paenian/sand-table/software/sand_trace/example_code/dog.JPG

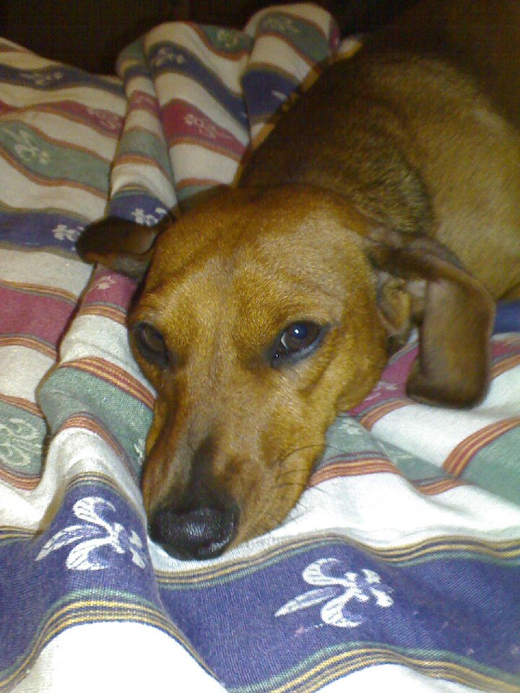
software/sand_trace/example_code/dog.JPG
