paenian/sand-table/software/sand_trace/example_code/dog.png

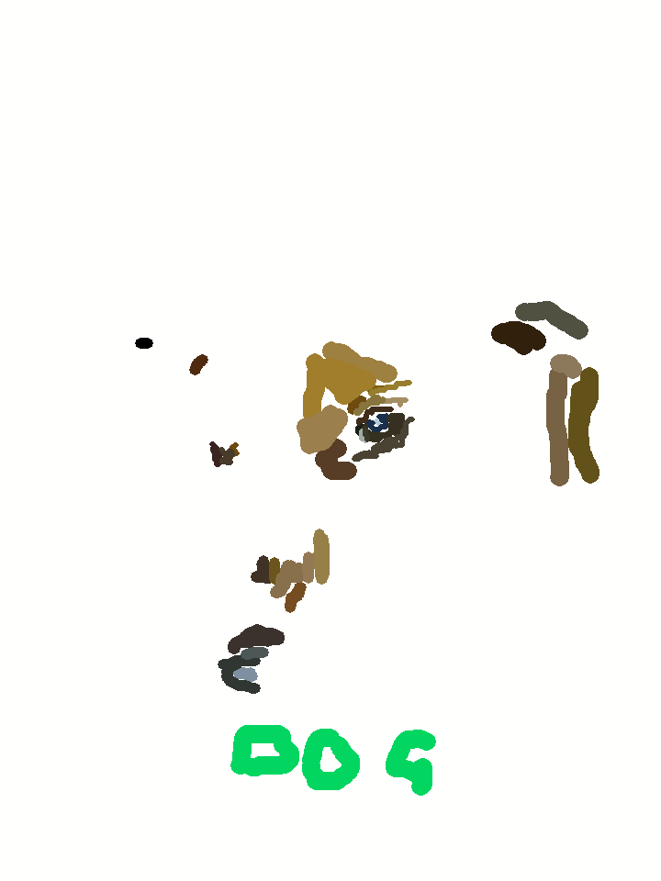
software/sand_trace/example_code/dog.png
