paenian/sand-table/software/sand_trace/example_code/loaddialog.png

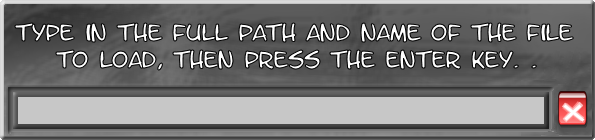
software/sand_trace/example_code/loaddialog.png
