paenian/sand-table/software/sand_trace/example_code/savedialog.png

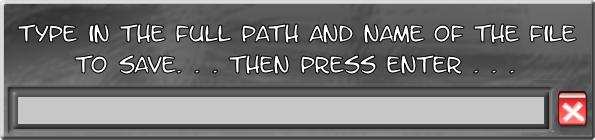
software/sand_trace/example_code/savedialog.png
