paenian/sand-table/software/sand_trace/example_code/screenshot.jpg

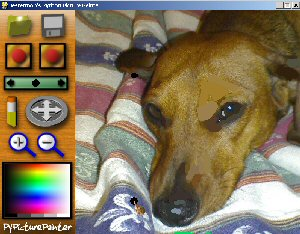
software/sand_trace/example_code/screenshot.jpg
