paenian/sand-table/software/sand_trace/example_code/toolbar.png

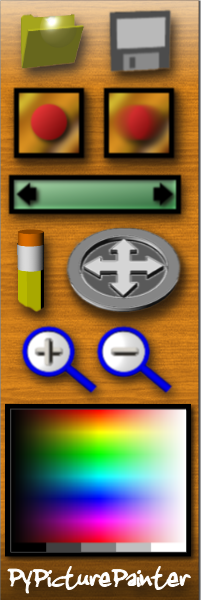
software/sand_trace/example_code/toolbar.png
