paenian/sand-table/hardware/glass_clamp.stl

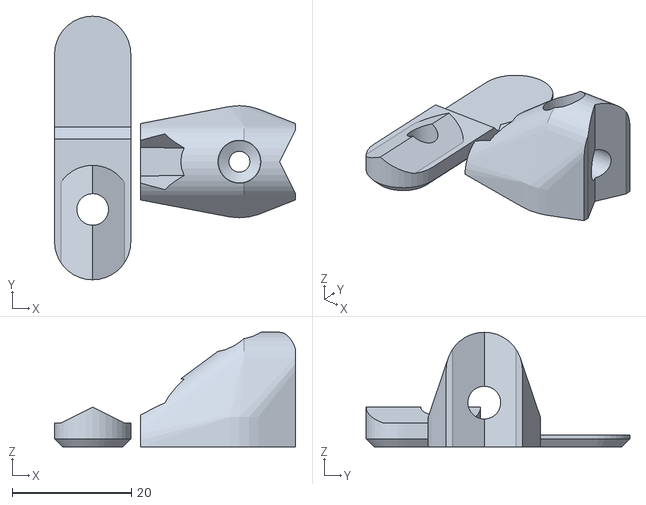
[picture p23: CAD file, 2018-05-06]
hardware/glass_clamp.stl
40.4 x 44.2 x 19.2
