paenian/sand-table/hardware/gravity_stls/string_pulley.stl

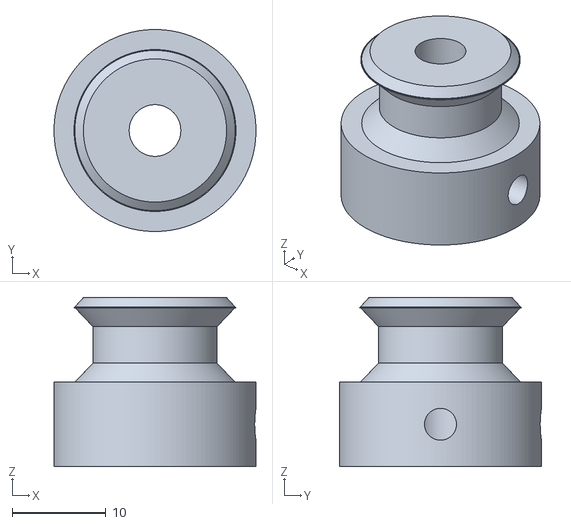
[picture p24: CAD file, 2017-11-30]
hardware/gravity_stls/string_pulley.stl
21.5 x 21.5 x 18.0
