paenian/sand-table/software/inkscape/share/extensions/Poly3DObjects/small_rhombicuboct.obj

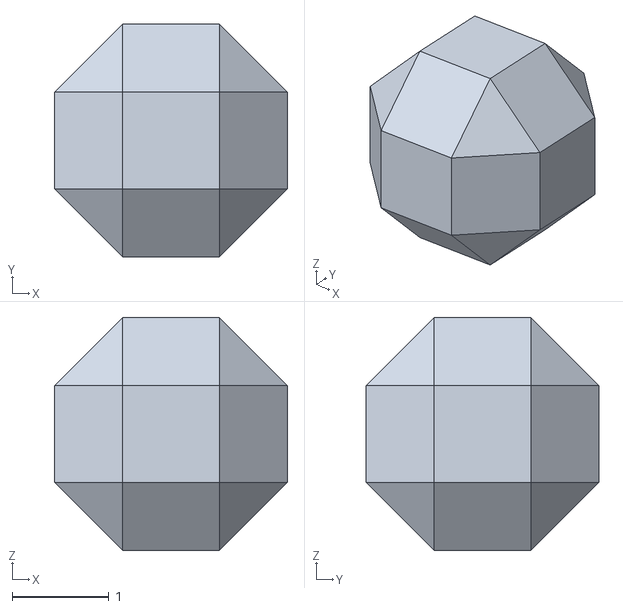
[picture p25: CAD file, 2018-03-14]
software/inkscape/share/extensions/Poly3DObjects/small_rhombicuboct.obj
2.41 x 2.41 x 2.41
