paenian/sand-table/hardware/crossbot_stls/offset_motor_mount.stl

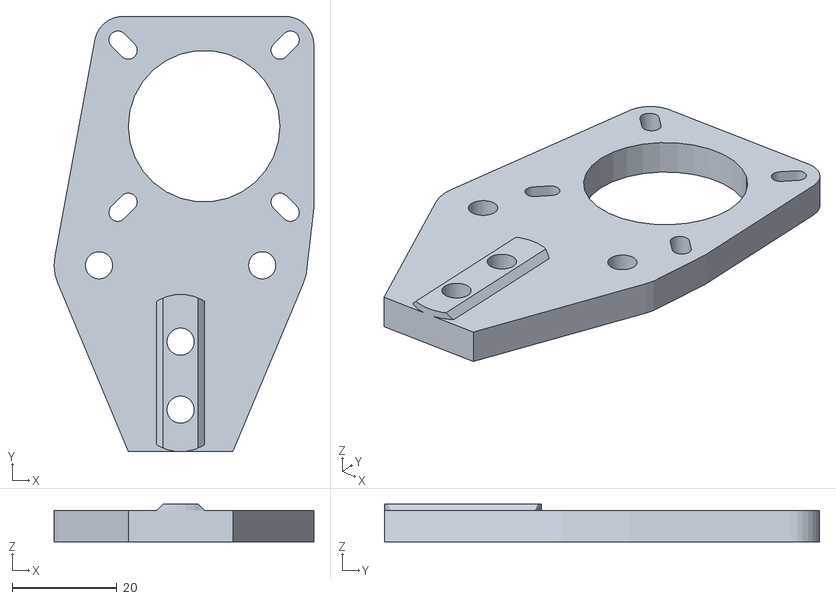
[picture p26: CAD file, 2018-03-14]
hardware/crossbot_stls/offset_motor_mount.stl
49.7 x 83.2 x 7.25
