paenian/sand-table/hardware/gravity_stls/weight_claw.stl

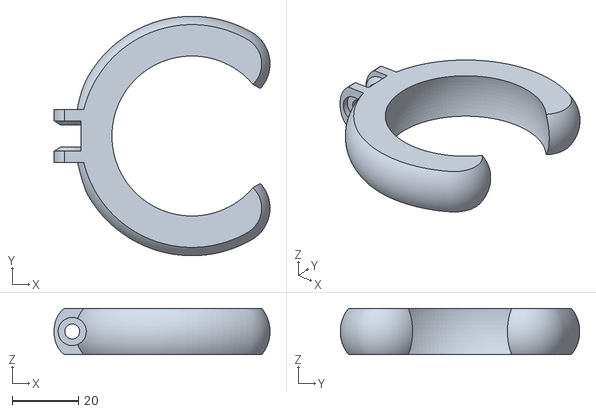
[picture p27: CAD file, 2017-11-16]
hardware/gravity_stls/weight_claw.stl
65.2 x 72.3 x 14.0
