paenian/sand-table/hardware/roundel.stl

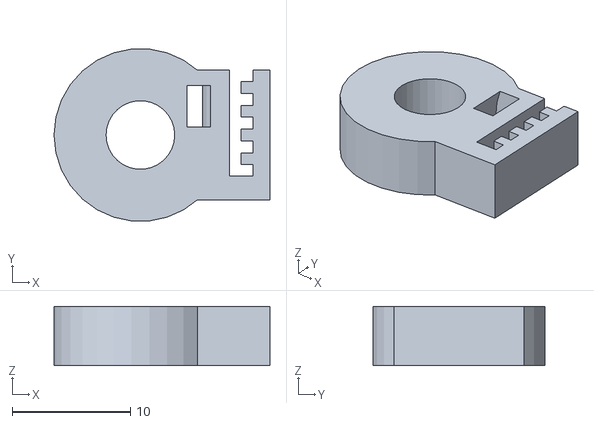
[picture p28: CAD file, 2018-04-22]
hardware/roundel.stl
18.2 x 14.5 x 5.00
