paenian/sand-table/software/inkscape/share/extensions/Poly3DObjects/trunc_tet.obj

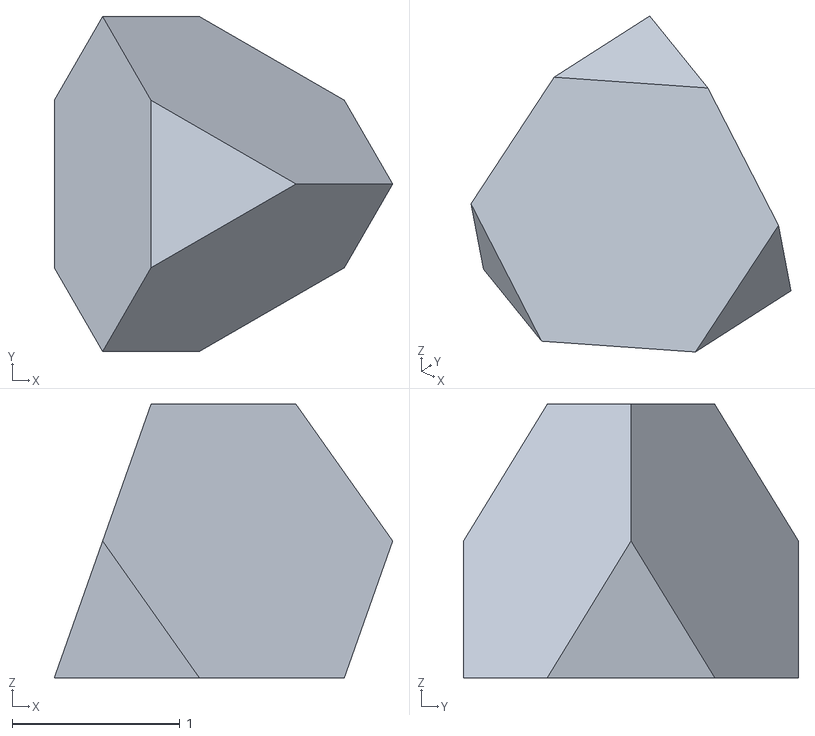
[picture p29: CAD file, 2018-03-14]
software/inkscape/share/extensions/Poly3DObjects/trunc_tet.obj
2.02 x 2.00 x 1.63
