paenian/sand-table/hardware/crossbot_stls/motor_mount.stl

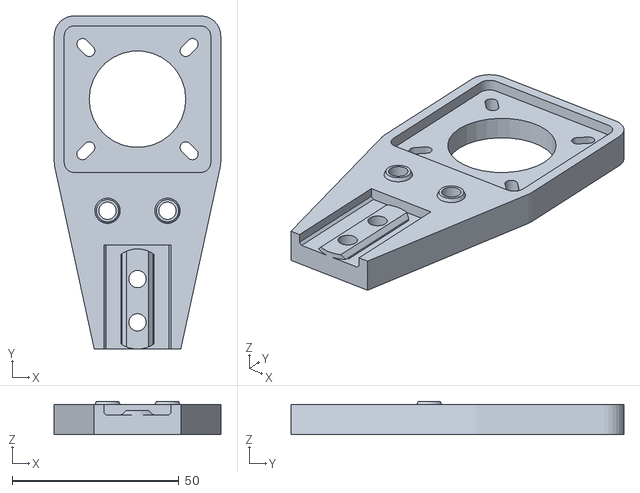
[picture p30: CAD file, 2018-03-14]
hardware/crossbot_stls/motor_mount.stl
50.0 x 100.0 x 10.0
