paenian/sand-table/hardware/gravity_stls/pulley.stl

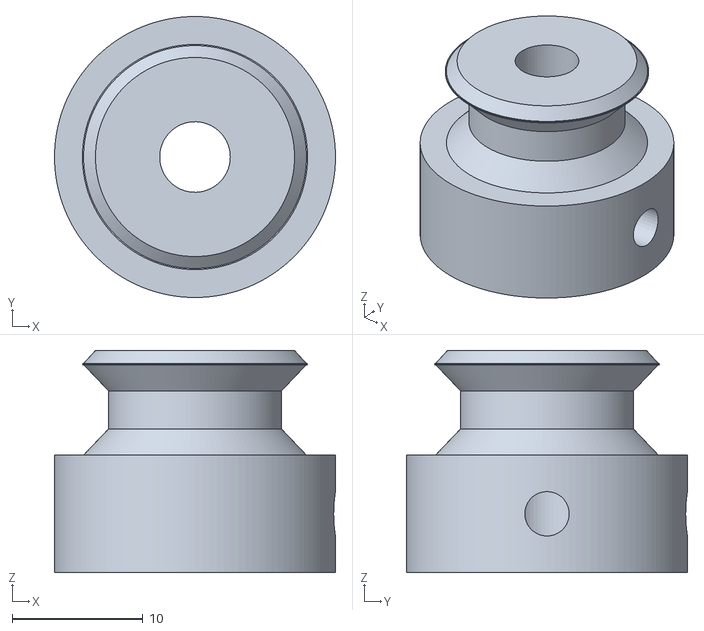
[picture p31: CAD file, 2017-11-16]
hardware/gravity_stls/pulley.stl
21.5 x 21.5 x 17.0
