paenian/sand-table/hardware/tri-carriage.stl

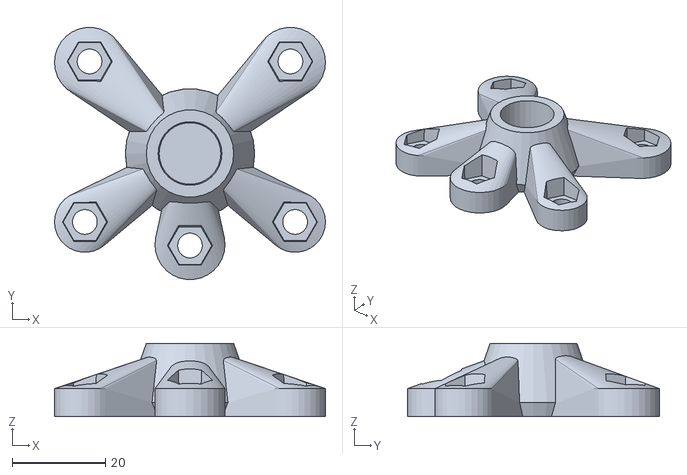
[picture p32: CAD file, 2018-04-22]
hardware/tri-carriage.stl
58.0 x 53.9 x 15.7
