paenian/sand-table/software/inkscape/share/extensions/Poly3DObjects/cuboct.obj

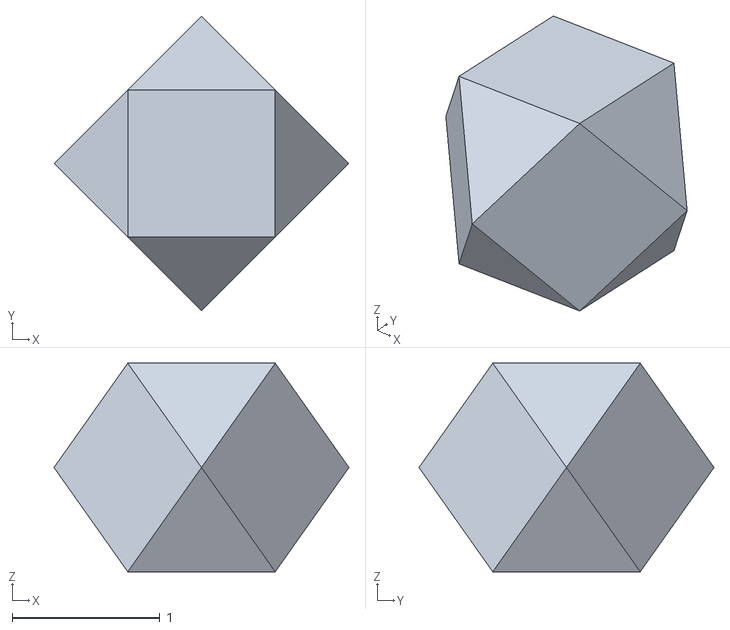
[picture p33: CAD file, 2018-03-14]
software/inkscape/share/extensions/Poly3DObjects/cuboct.obj
2.00 x 2.00 x 1.41
