paenian/sand-table/hardware/cross_idler.stl

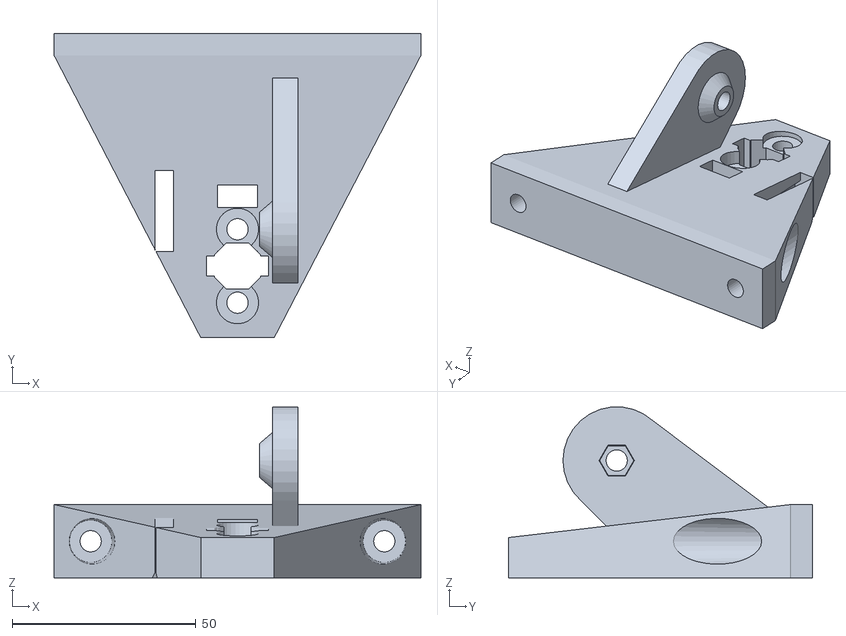
[picture p34: CAD file, 2018-04-20]
hardware/cross_idler.stl
100.0 x 82.9 x 46.6
