paenian/sand-table/hardware/crossbot_stls/base_beam_mount.stl

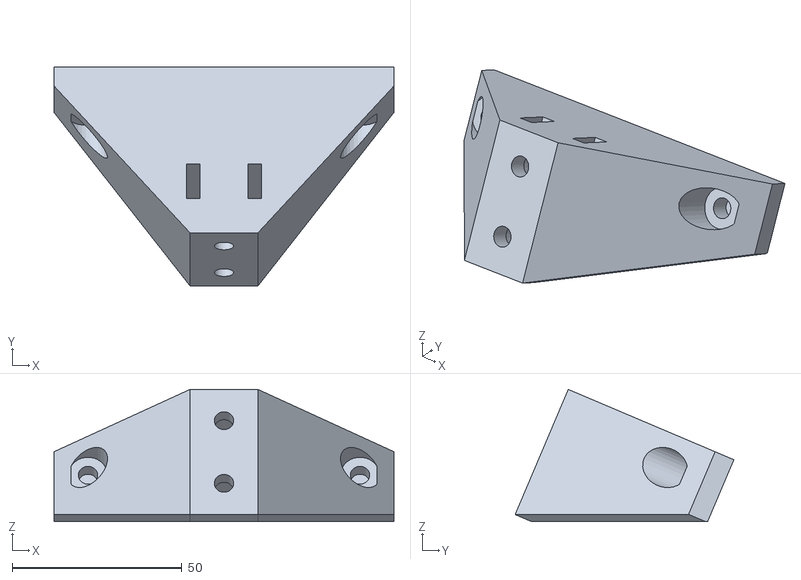
[picture p35: CAD file, 2018-03-14]
hardware/crossbot_stls/base_beam_mount.stl
100.0 x 64.4 x 38.9
