paenian/sand-table/hardware/gravity_stls/magnet_mount_3-8.stl

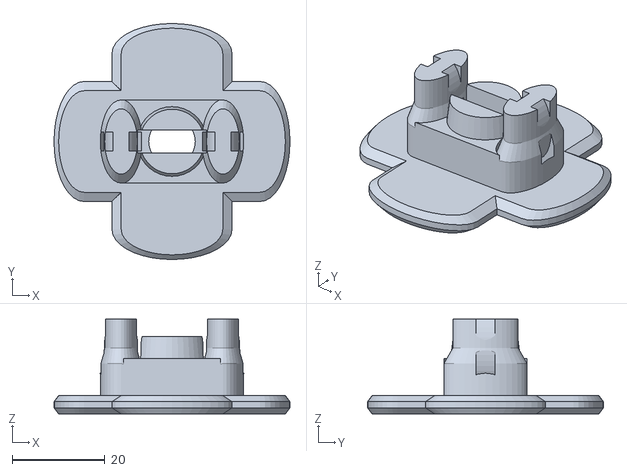
[picture p36: CAD file, 2017-11-15]
hardware/gravity_stls/magnet_mount_3-8.stl
51.0 x 51.0 x 20.5
