paenian/sand-table/software/inkscape/share/extensions/Poly3DObjects/small_triam_icos.obj

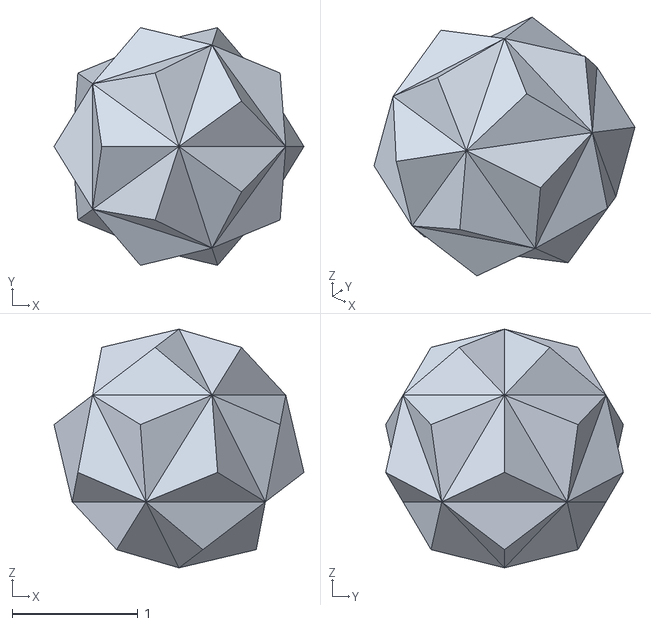
[picture p37: CAD file, 2018-03-14]
software/inkscape/share/extensions/Poly3DObjects/small_triam_icos.obj
1.99 x 1.89 x 1.90
