paenian/sand-table/hardware/cross_motor.stl

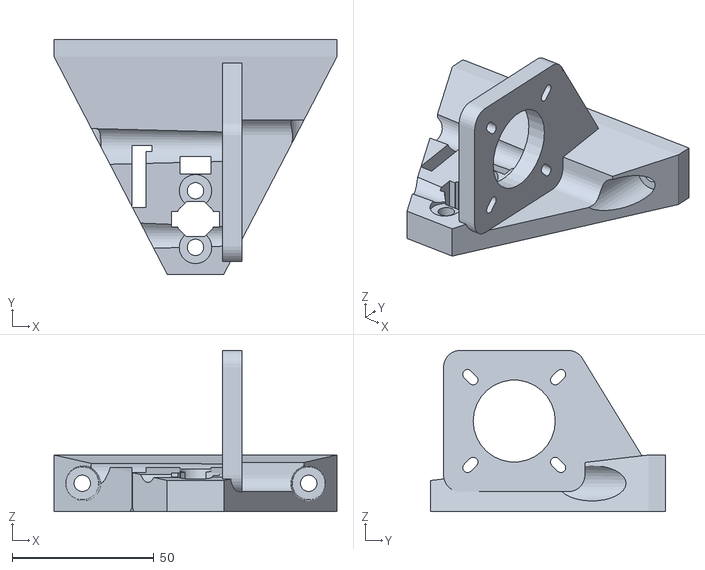
[picture p38: CAD file, 2018-04-20]
hardware/cross_motor.stl
100.0 x 82.9 x 57.0
