paenian/sand-table/hardware/crossbot_stls/double_idler.stl

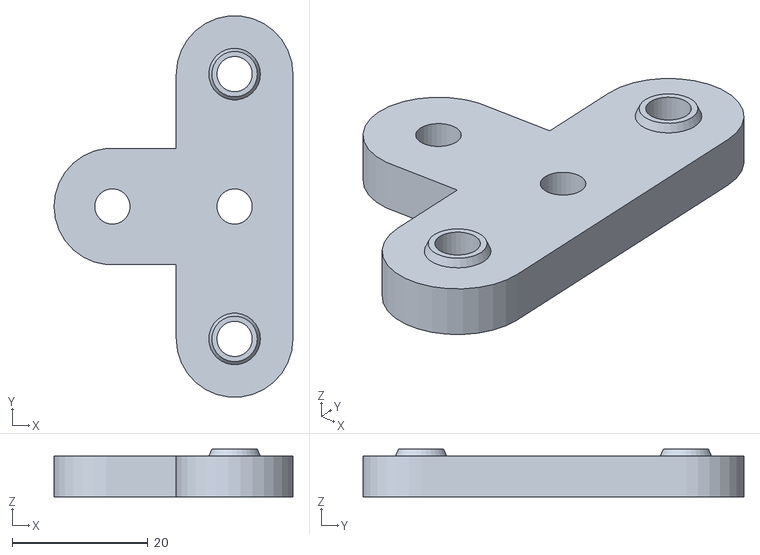
[picture p39: CAD file, 2018-03-14]
hardware/crossbot_stls/double_idler.stl
35.2 x 56.1 x 7.00
