paenian/sand-table/hardware/gravity_stls/belt_pulley.stl

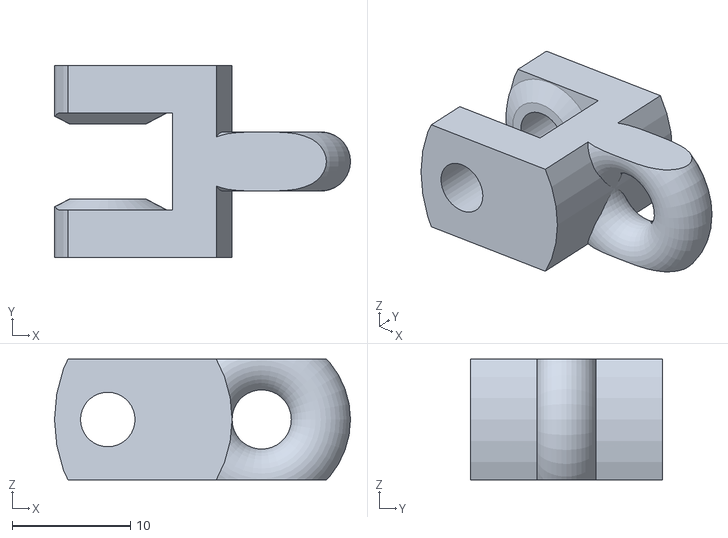
[picture p40: CAD file, 2017-11-15]
hardware/gravity_stls/belt_pulley.stl
25.0 x 16.2 x 10.2
