paenian/sand-table/software/inkscape/share/extensions/Poly3DObjects/great_rhombicosidodec.obj

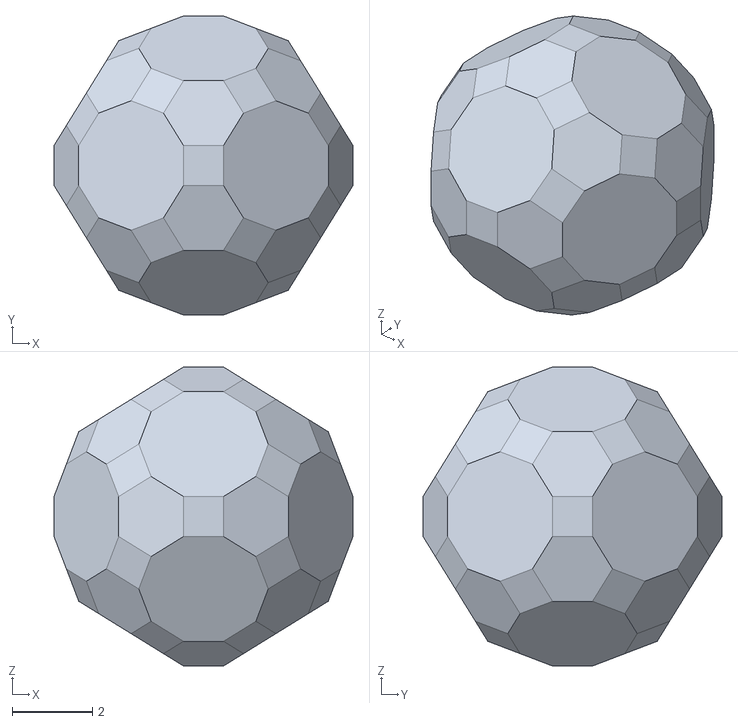
[picture p41: CAD file, 2018-03-14]
software/inkscape/share/extensions/Poly3DObjects/great_rhombicosidodec.obj
7.47 x 7.47 x 7.47
