paenian/sand-table/hardware/gravity_stls/idler_weight_corner.stl

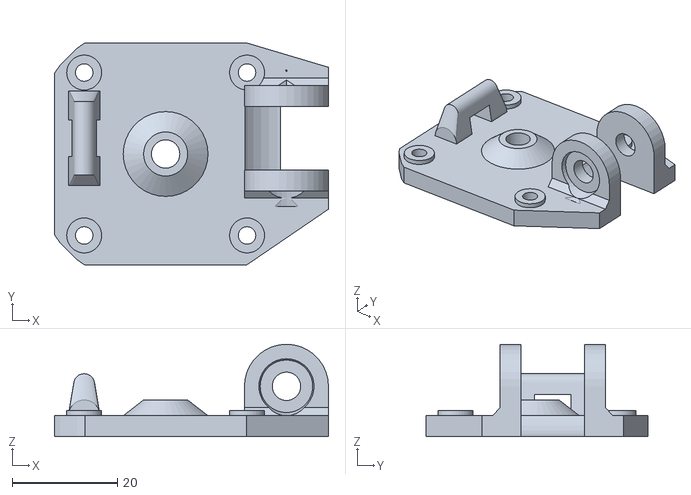
[picture p42: CAD file, 2017-09-14]
hardware/gravity_stls/idler_weight_corner.stl
52.1 x 42.3 x 17.6
