paenian/sand-table/hardware/roundel_2.stl

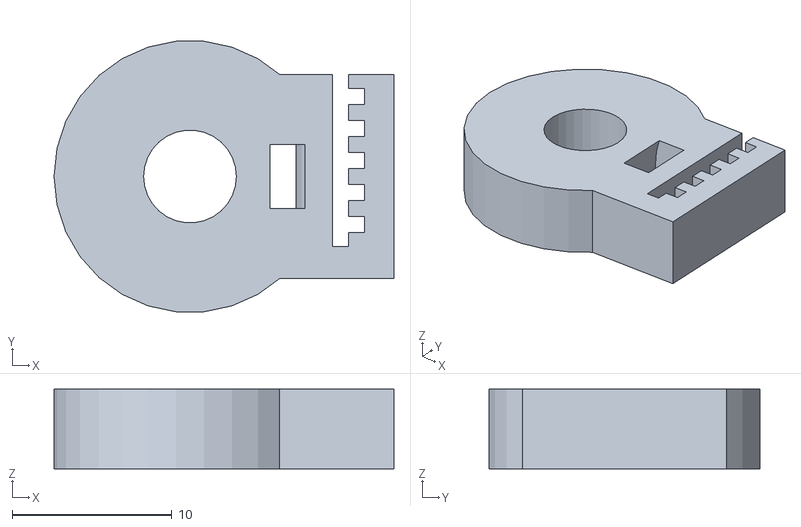
[picture p43: CAD file, 2018-04-13]
hardware/roundel_2.stl
21.2 x 16.9 x 5.00
