paenian/sand-table/software/inkscape/share/extensions/Poly3DObjects/trunc_oct.obj

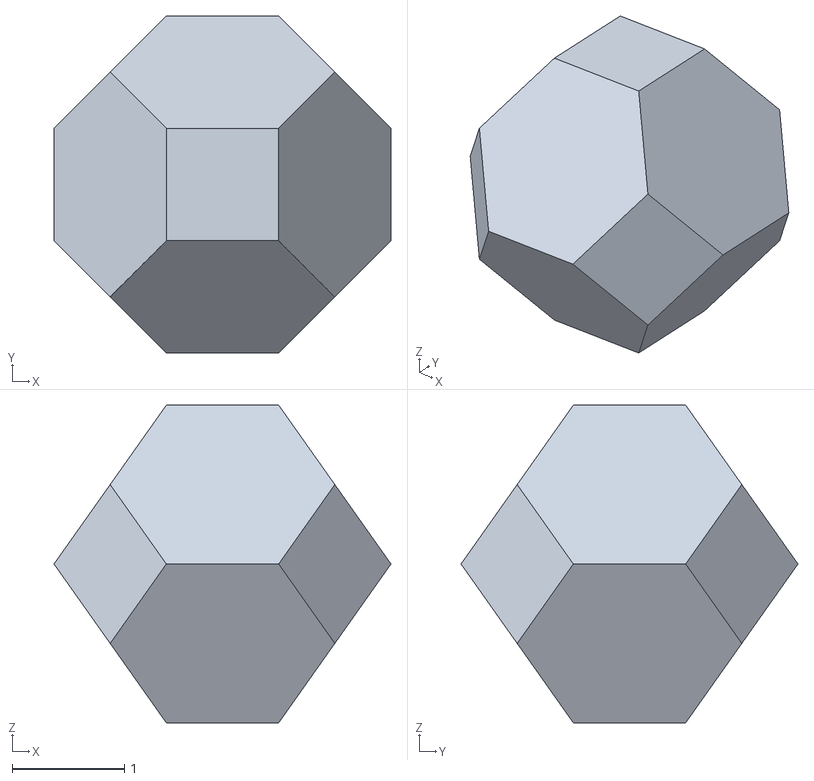
[picture p44: CAD file, 2018-03-14]
software/inkscape/share/extensions/Poly3DObjects/trunc_oct.obj
3.00 x 3.00 x 2.83
