paenian/sand-table/hardware/idler_mount_2.stl

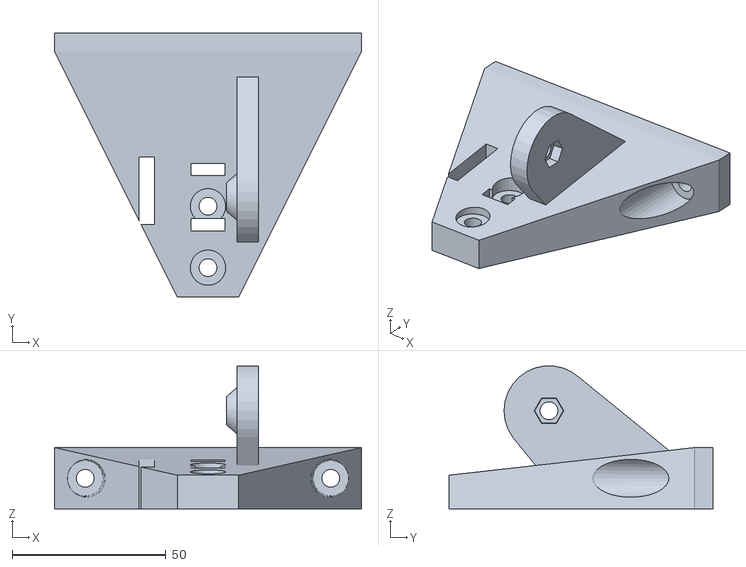
[picture p45: CAD file, 2018-04-13]
hardware/idler_mount_2.stl
100.0 x 85.9 x 46.6
