paenian/sand-table/software/inkscape/share/extensions/Poly3DObjects/icosidodec.obj

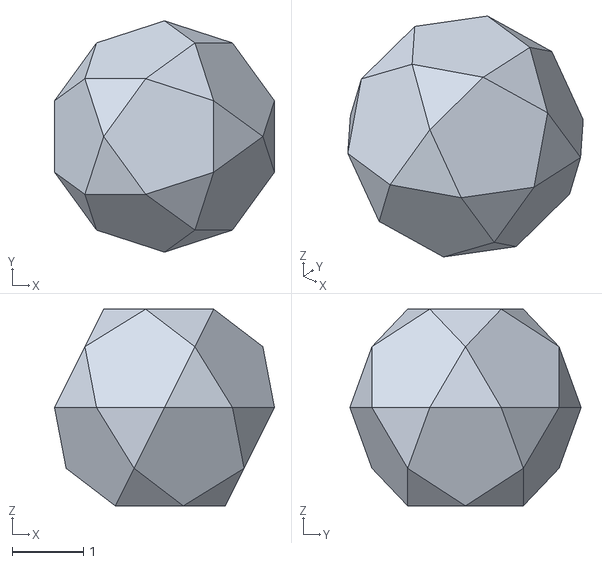
[picture p46: CAD file, 2018-03-14]
software/inkscape/share/extensions/Poly3DObjects/icosidodec.obj
3.08 x 3.24 x 2.75
