paenian/sand-table/hardware/motor_mount_2.stl

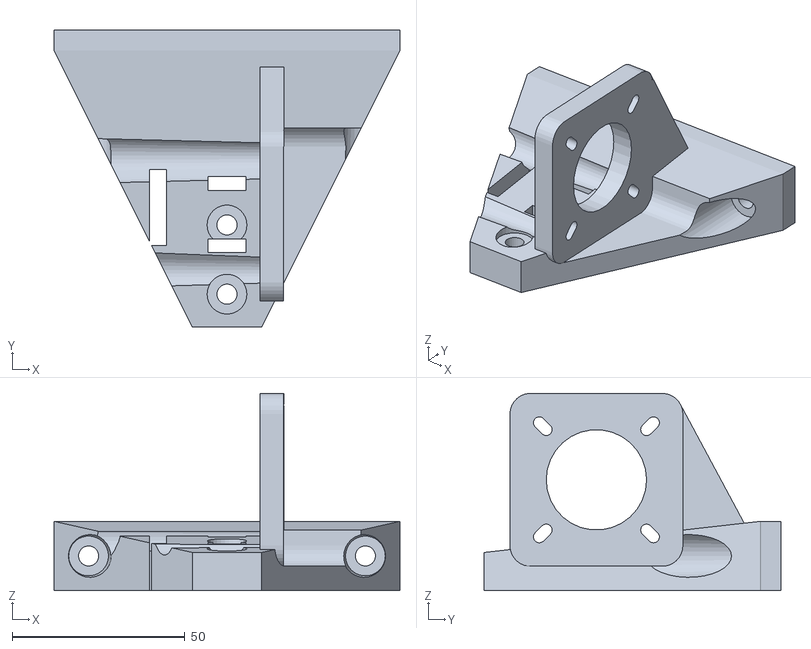
[picture p48: CAD file, 2018-04-13]
hardware/motor_mount_2.stl
100.0 x 85.9 x 57.0
