paenian/sand-table/software/inkscape/share/extensions/Poly3DObjects/jessens_orthog_icos.obj

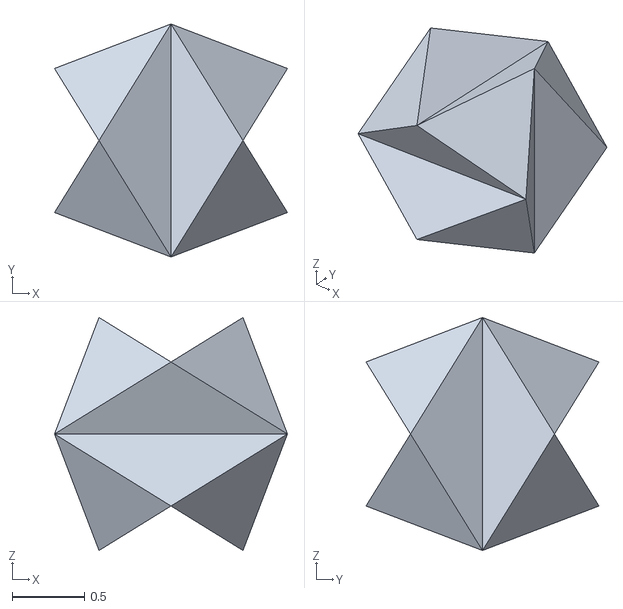
[picture p49: CAD file, 2018-03-14]
software/inkscape/share/extensions/Poly3DObjects/jessens_orthog_icos.obj
1.62 x 1.62 x 1.62
