paenian/sand-table/hardware/glass_clamp_base.stl

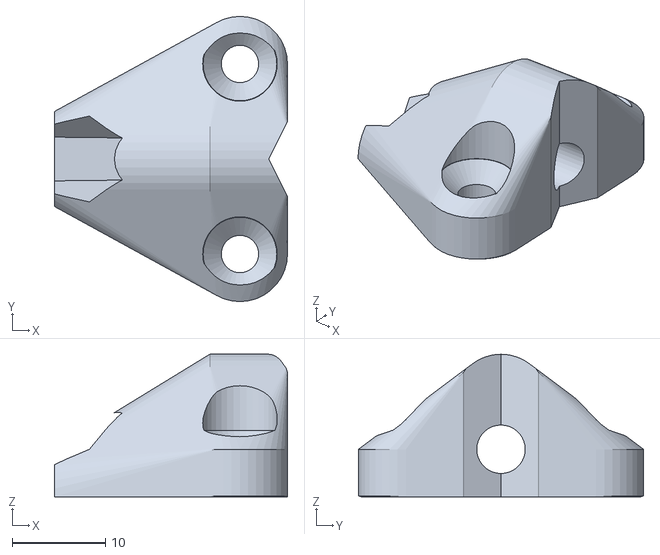
[picture p50: CAD file, 2018-04-04]
hardware/glass_clamp_base.stl
25.0 x 30.6 x 15.3
