paenian/sand-table/hardware/gravity_stls/drill_guide.stl

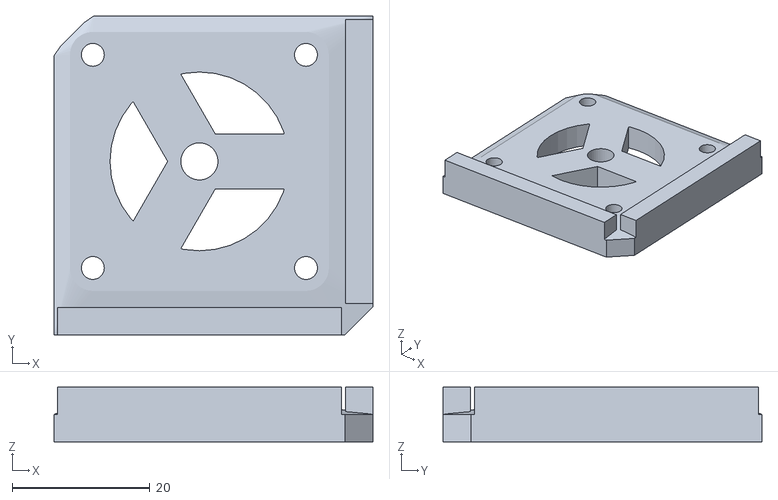
[picture p51: CAD file, 2017-09-11]
hardware/gravity_stls/drill_guide.stl
46.4 x 46.4 x 8.00
