paenian/sand-table/software/inkscape/share/extensions/Poly3DObjects/trunc_icos.obj

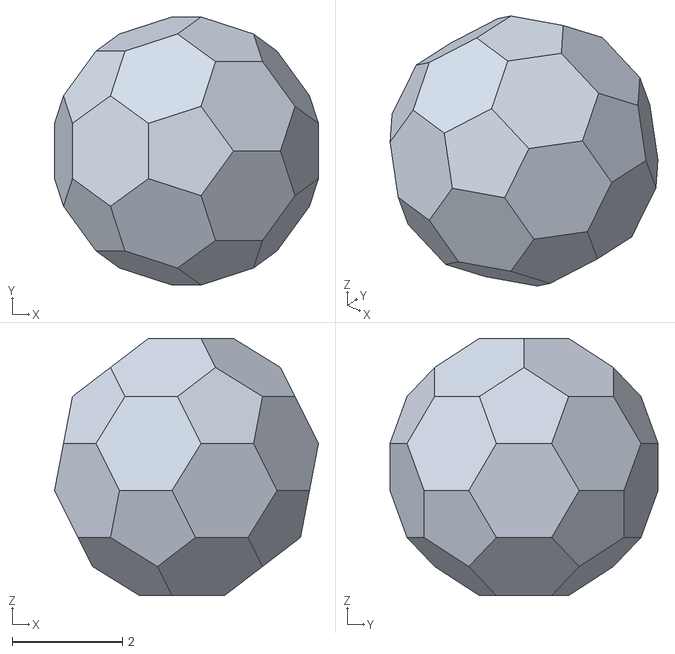
[picture p52: CAD file, 2018-03-14]
software/inkscape/share/extensions/Poly3DObjects/trunc_icos.obj
4.78 x 4.85 x 4.65
