paenian/sand-table/hardware/glass_clamp_lever.stl

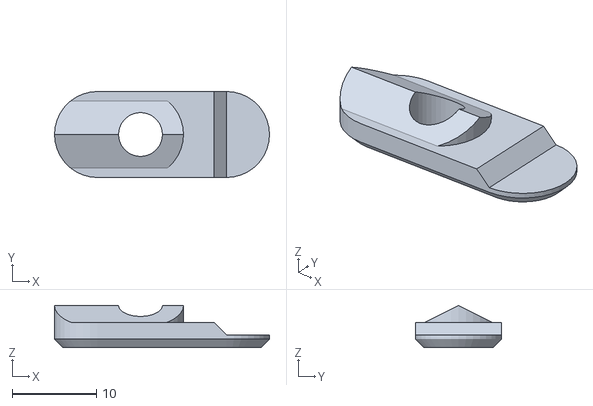
[picture p53: CAD file, 2018-04-04]
hardware/glass_clamp_lever.stl
25.5 x 10.2 x 5.00
