paenian/sand-table/hardware/gravity_stls/belt_clamp.stl

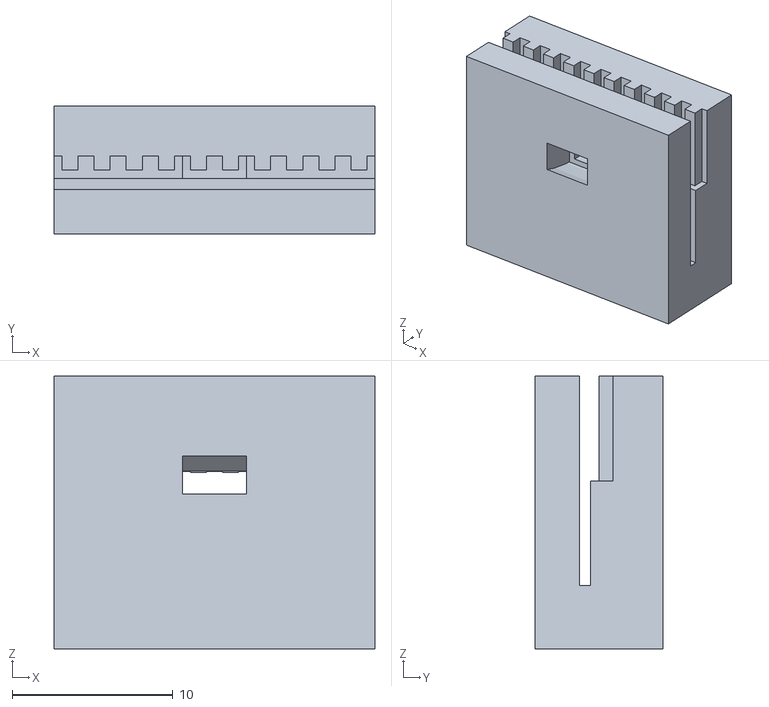
[picture p54: CAD file, 2017-09-11]
hardware/gravity_stls/belt_clamp.stl
20.0 x 8.00 x 17.0
