paenian/sand-table/software/inkscape/share/extensions/Poly3DObjects/rhomb_triacont.obj

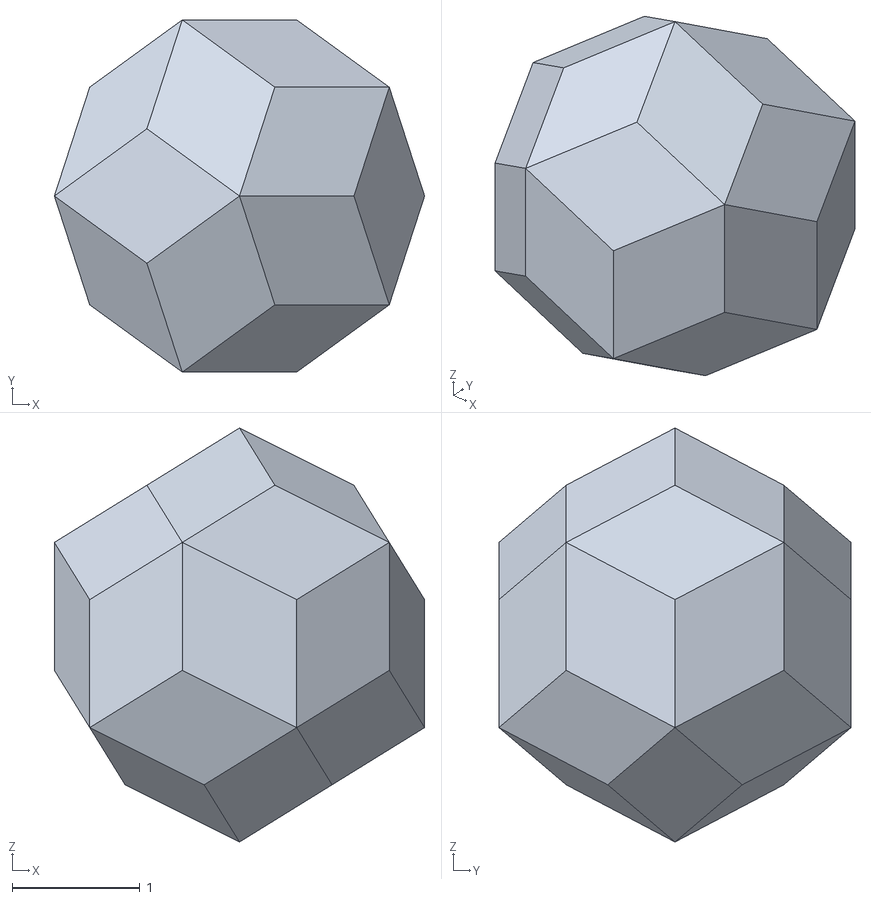
[picture p55: CAD file, 2018-03-14]
software/inkscape/share/extensions/Poly3DObjects/rhomb_triacont.obj
2.89 x 2.75 x 3.24
