paenian/sand-table/hardware/gravity_stls/spring_roller.stl

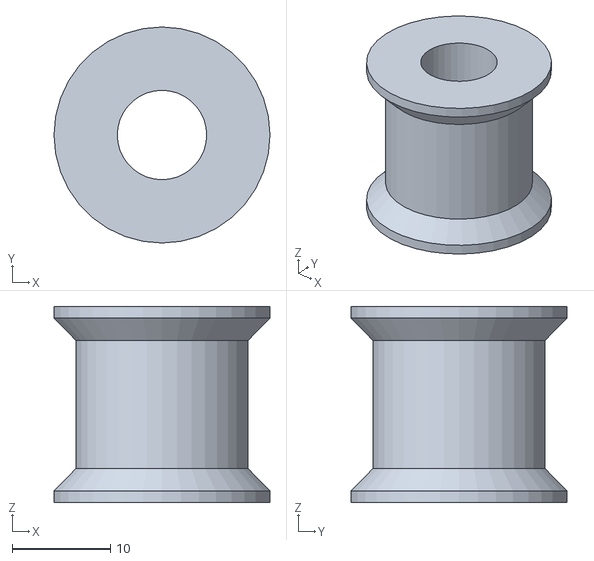
[picture p56: CAD file, 2017-09-11]
hardware/gravity_stls/spring_roller.stl
22.0 x 22.0 x 20.0
