paenian/sand-table/hardware/PM_UNO_base_fan_holder.stl

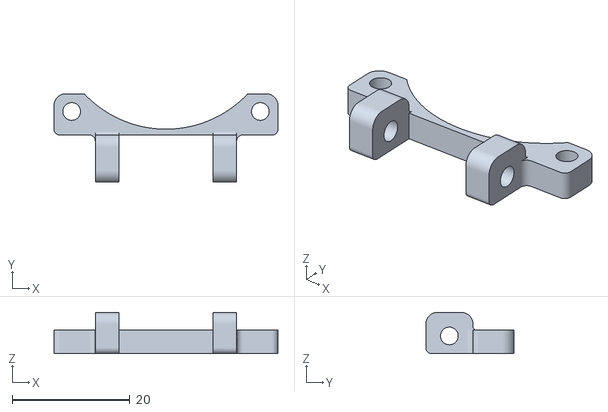
[picture p57: CAD file, 2018-03-05]
hardware/PM_UNO_base_fan_holder.stl
38.0 x 15.0 x 7.00
