paenian/sand-table/software/inkscape/share/extensions/Poly3DObjects/oct.obj

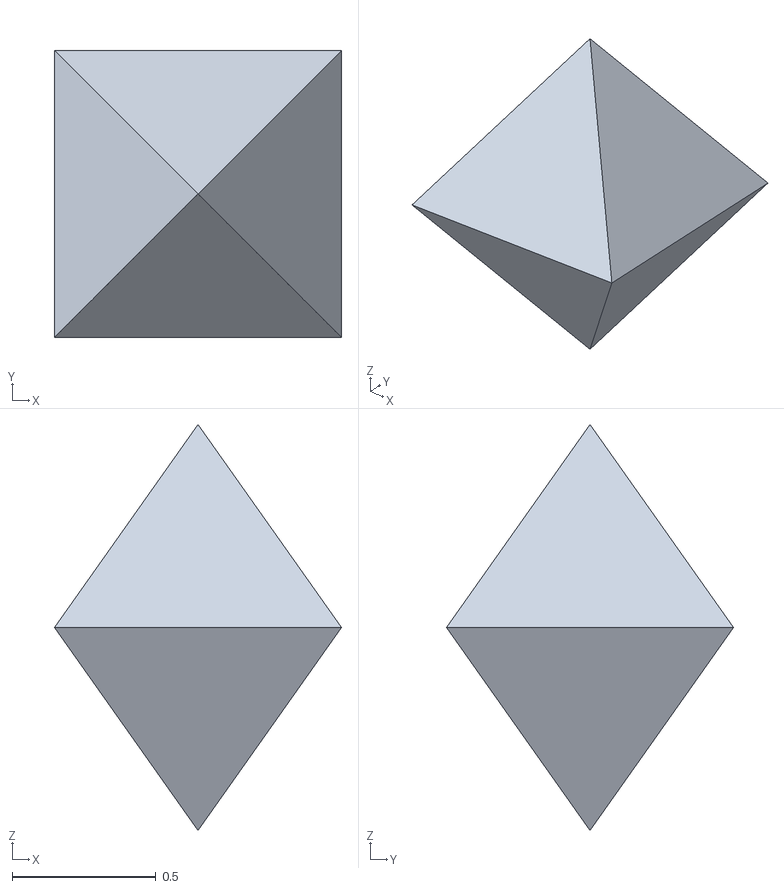
[picture p58: CAD file, 2018-03-14]
software/inkscape/share/extensions/Poly3DObjects/oct.obj
1.00 x 1.00 x 1.41
