paenian/sand-table/hardware/gravity_stls/idler_corner.stl

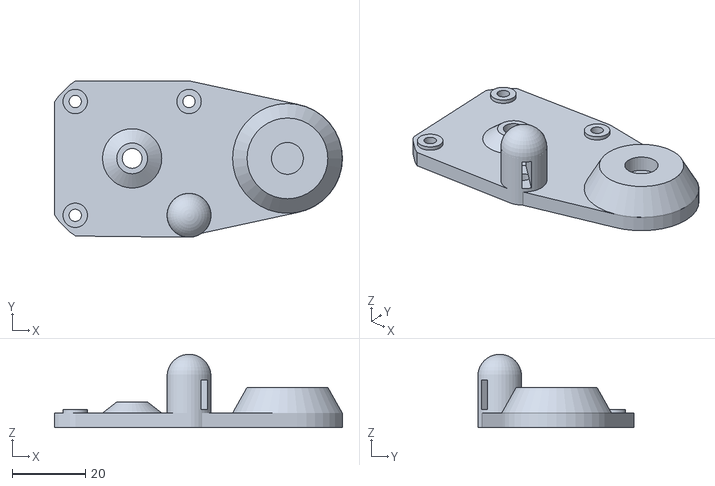
[picture p59: CAD file, 2017-09-11]
hardware/gravity_stls/idler_corner.stl
78.4 x 42.6 x 20.0
