paenian/sand-table/hardware/PM_uno_mount_fan_mod.stl

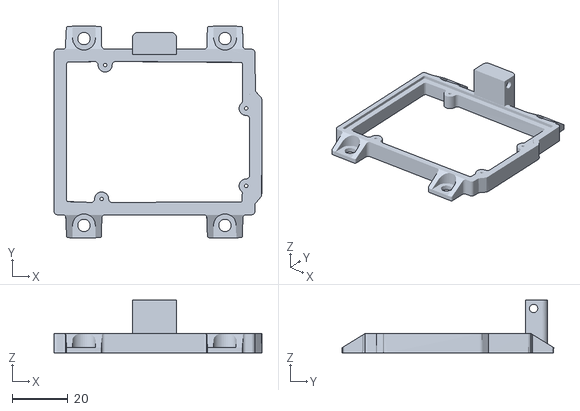
[picture p60: CAD file, 2018-03-05]
hardware/PM_uno_mount_fan_mod.stl
74.9 x 76.2 x 19.0
