paenian/sand-table/software/inkscape/share/extensions/Poly3DObjects/rhomb_dodec.obj

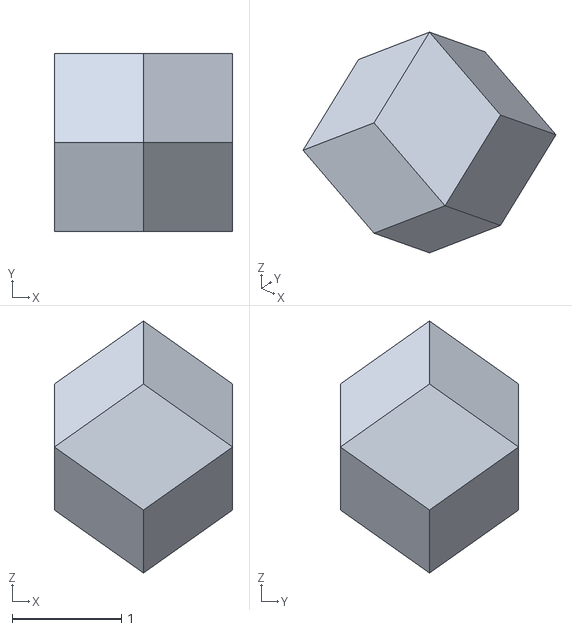
[picture p61: CAD file, 2018-03-14]
software/inkscape/share/extensions/Poly3DObjects/rhomb_dodec.obj
1.63 x 1.63 x 2.31
