paenian/sand-table/hardware/gravity_stls/magnet_mount.stl

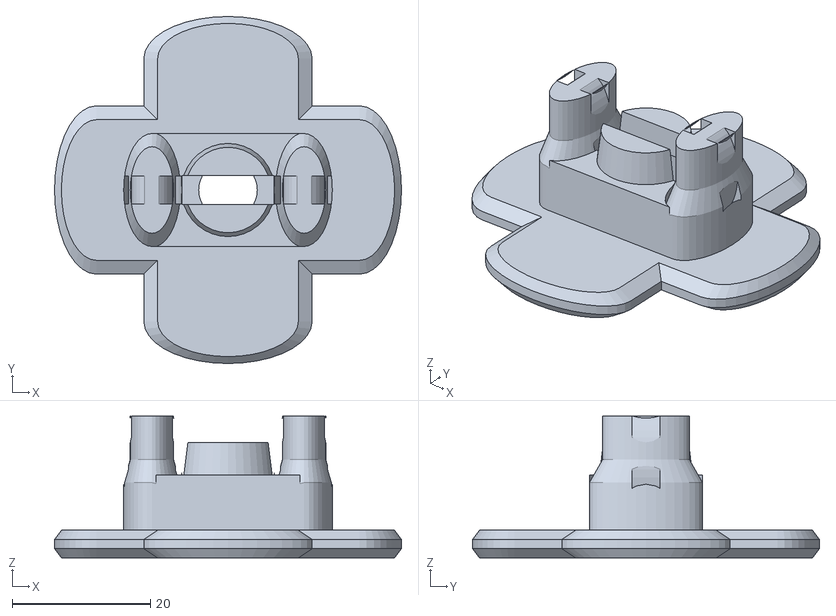
[picture p62: CAD file, 2017-09-11]
hardware/gravity_stls/magnet_mount.stl
50.2 x 50.2 x 20.5
