paenian/sand-table/software/inkscape/share/extensions/Poly3DObjects/snub_cube.obj

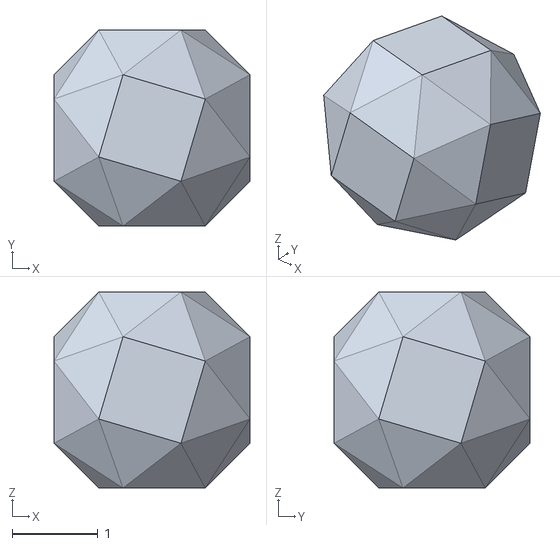
[picture p63: CAD file, 2018-03-14]
software/inkscape/share/extensions/Poly3DObjects/snub_cube.obj
2.29 x 2.29 x 2.29
