paenian/sand-table/software/inkscape/share/extensions/Poly3DObjects/cube.obj

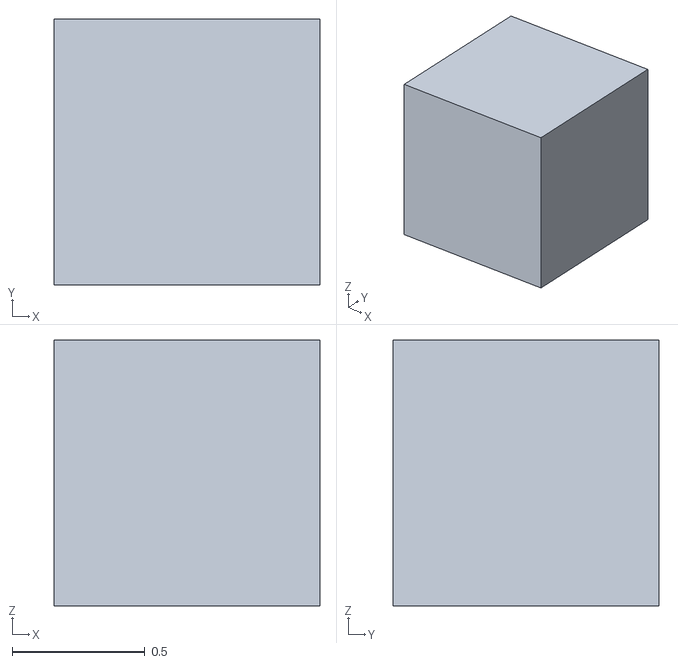
[picture p65: CAD file, 2018-03-14]
software/inkscape/share/extensions/Poly3DObjects/cube.obj
1.00 x 1.00 x 1.00
