paenian/sand-table/software/inkscape/share/extensions/Poly3DObjects/great_stel_dodec.obj

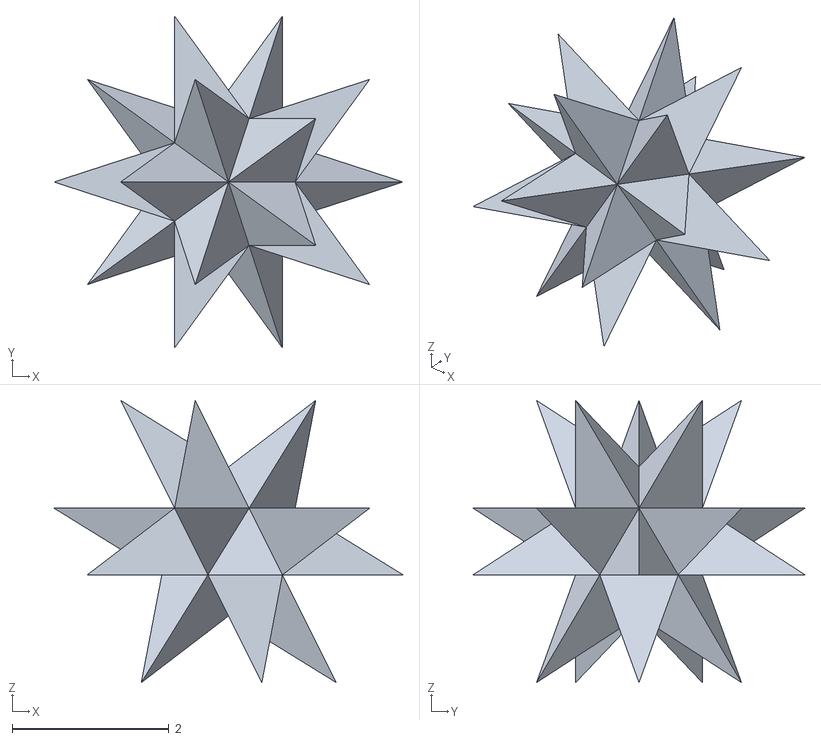
[picture p66: CAD file, 2018-03-14]
software/inkscape/share/extensions/Poly3DObjects/great_stel_dodec.obj
4.45 x 4.24 x 3.60
