paenian/sand-table/software/inkscape/share/extensions/Poly3DObjects/snub_dodec.obj

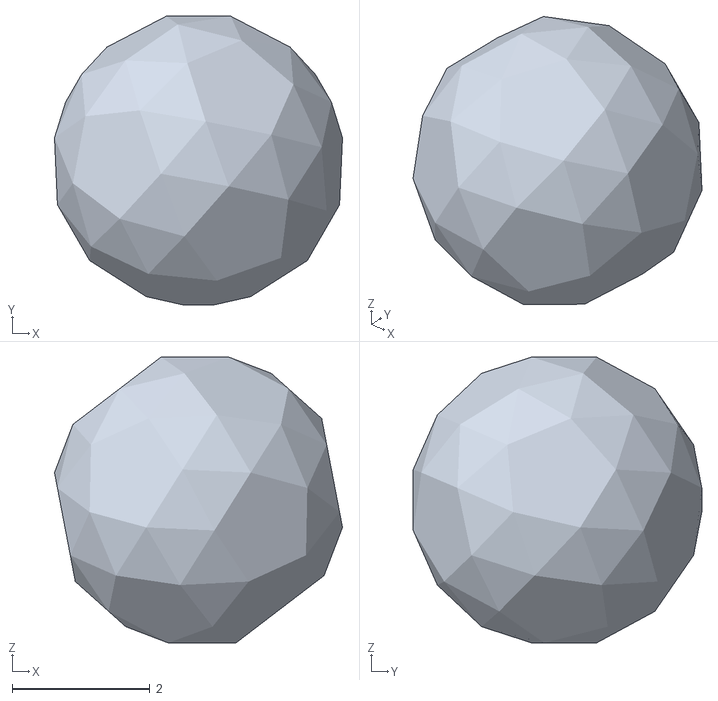
[picture p67: CAD file, 2018-03-14]
software/inkscape/share/extensions/Poly3DObjects/snub_dodec.obj
4.19 x 4.19 x 4.15
