paenian/sand-table/software/inkscape/share/extensions/Poly3DObjects/tet.obj

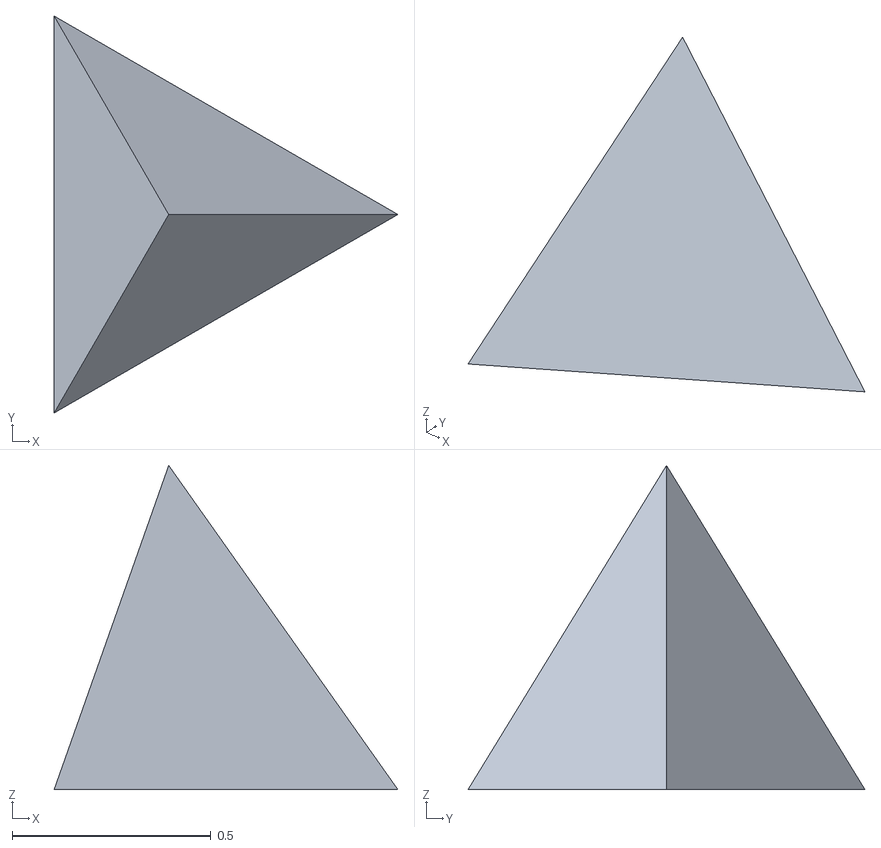
[picture p68: CAD file, 2018-03-14]
software/inkscape/share/extensions/Poly3DObjects/tet.obj
0.866 x 1.00 x 0.816
