paenian/sand-table/software/inkscape/share/extensions/Poly3DObjects/small_rhombicosidodec.obj

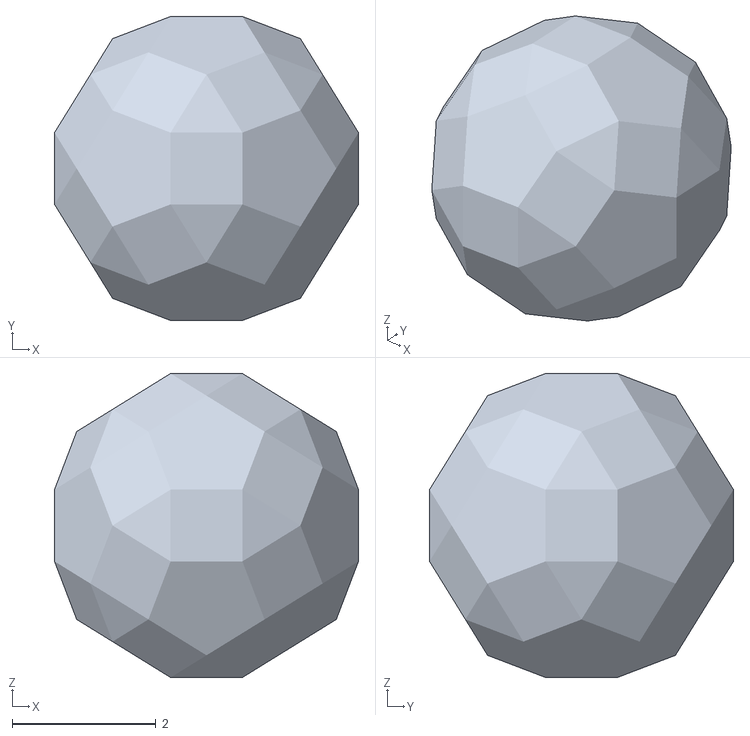
[picture p69: CAD file, 2018-03-14]
software/inkscape/share/extensions/Poly3DObjects/small_rhombicosidodec.obj
4.24 x 4.24 x 4.24
