paenian/sand-table/software/inkscape/share/extensions/Poly3DObjects/dodec.obj

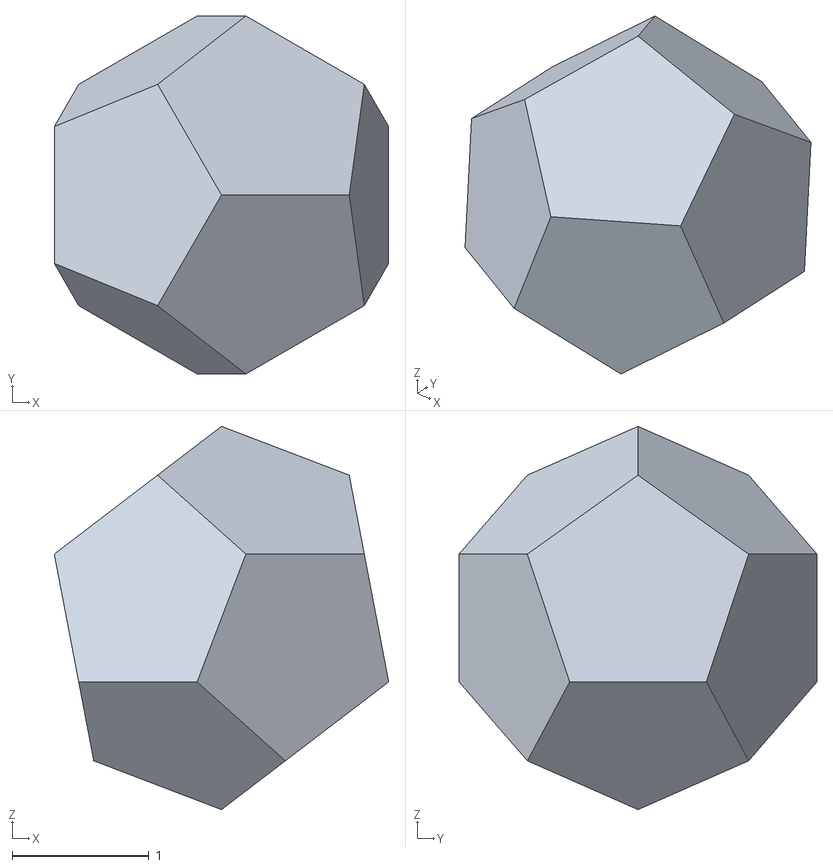
[picture p70: CAD file, 2018-03-14]
software/inkscape/share/extensions/Poly3DObjects/dodec.obj
2.45 x 2.62 x 2.80
