paenian/sand-table/software/inkscape/share/extensions/Poly3DObjects/icos.obj

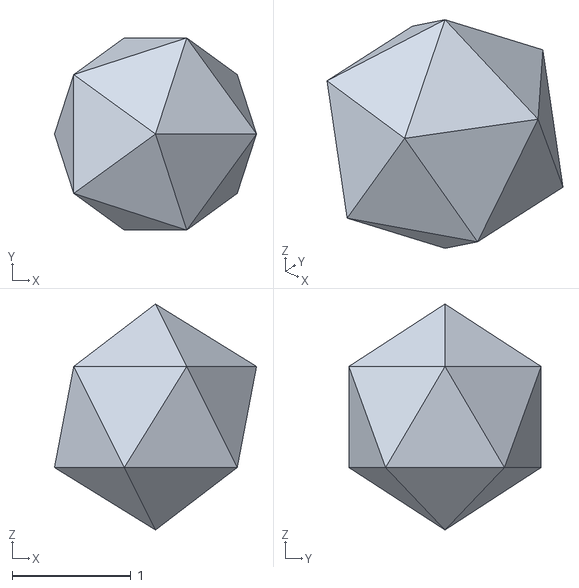
[picture p71: CAD file, 2018-03-14]
software/inkscape/share/extensions/Poly3DObjects/icos.obj
1.70 x 1.62 x 1.90
