paenian/sand-table/software/inkscape/share/extensions/Poly3DObjects/great_dodec.obj

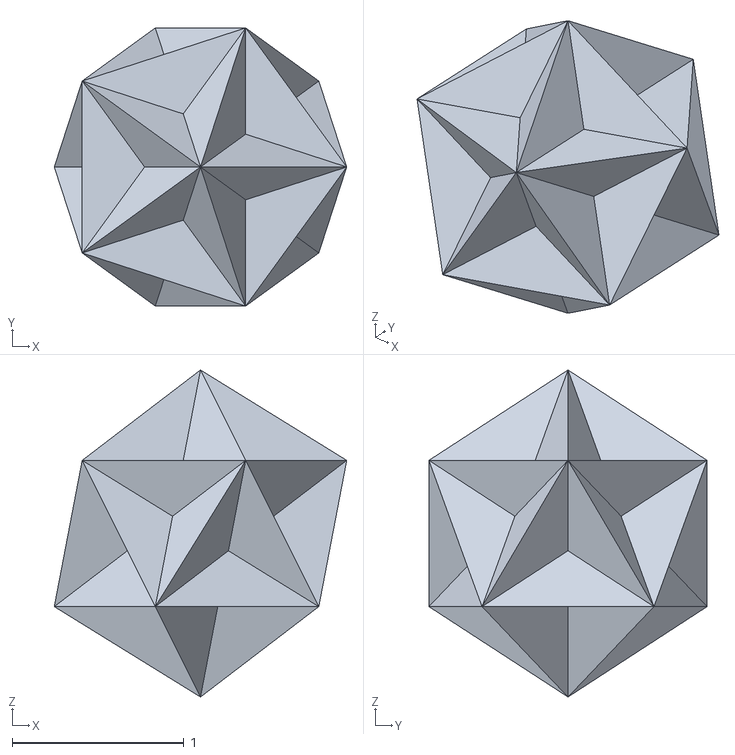
[picture p72: CAD file, 2018-03-14]
software/inkscape/share/extensions/Poly3DObjects/great_dodec.obj
1.70 x 1.62 x 1.90
