paenian/sand-table/software/inkscape/share/extensions/Poly3DObjects/trunc_cube.obj

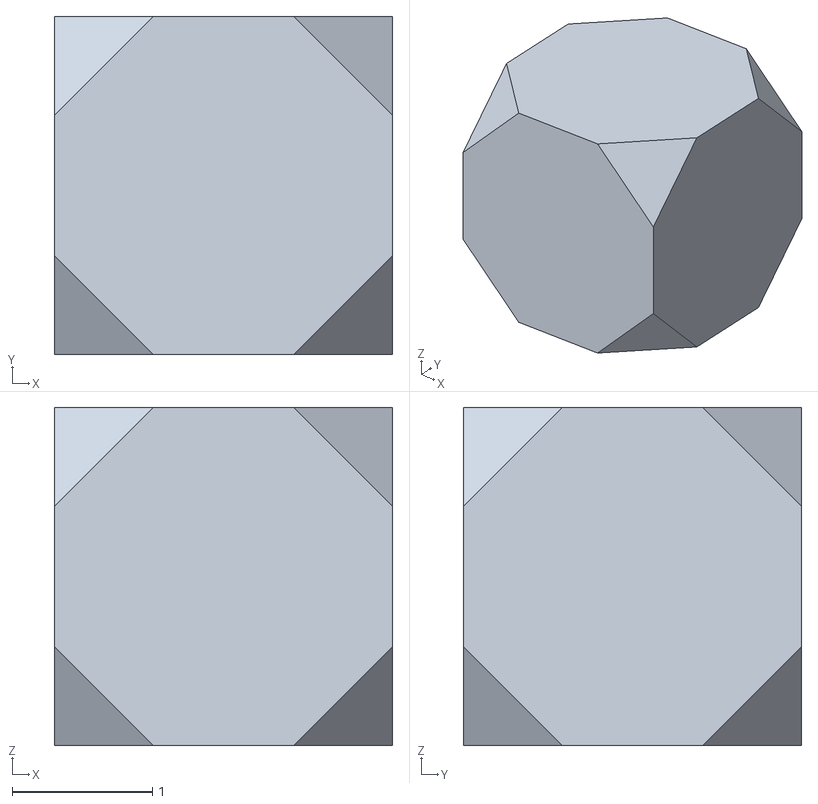
[picture p73: CAD file, 2018-03-14]
software/inkscape/share/extensions/Poly3DObjects/trunc_cube.obj
2.41 x 2.41 x 2.41
