paenian/sand-table/software/inkscape/share/extensions/Poly3DObjects/trunc_dodec.obj

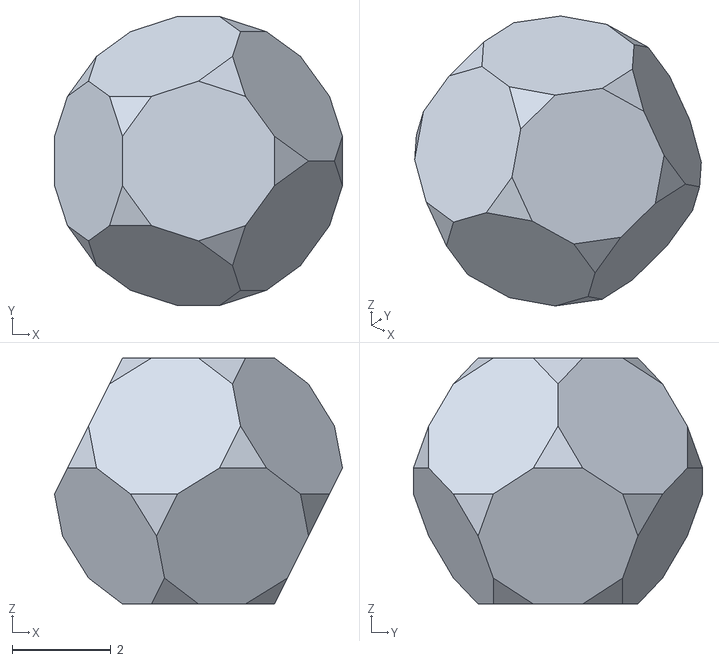
[picture p74: CAD file, 2018-03-14]
software/inkscape/share/extensions/Poly3DObjects/trunc_dodec.obj
5.83 x 5.85 x 4.98
