paenian/sand-table/software/sand_trace/gcode_sender.py

#!/usr/bin/env python
# -*- coding: utf-8 -*-

import serial
import time
import random
import math

__author__ = 'Paul Chase'

class Gcode_Sender(object):
    MOTOR_DIST = 417

    def __init__(self):
        self.serial = serial.Serial('/dev/ttyACM1', 115200)

        # Wake up grbl
        self.serial.write("\r\n\r\n")
        time.sleep(2)  # Wait for grbl to initialize
        self.serial.flushInput()  # Flush startup text in serial input

        # Stream g-code to grbl
        for x in range(0, 10):
            self.send_move(50, 50)
            self.send_move(50, -50)
            self.send_move(-50, -50)
            self.send_move(-50, 50)

        self.serial.close()

    def send_move(self, x, y):
        dist = self.MOTOR_DIST
        print('Converting: ( ' + str(x) + " , " + str(y) + ' )')

        a = math.sqrt(x * x + y * y)
        b = math.sqrt(x * x + (dist - y) * (dist - y))

        move = "G0 X" + str(a) + " Y" + str(b)

        print('Sending: ' + move)
        self.serial.write(move + '\n')
        self.grbl_out = self.serial.readline()
        print(' : ' + move.strip())
